indifferentengine/JankyTapeEcho/STL/Transport Mount.stl

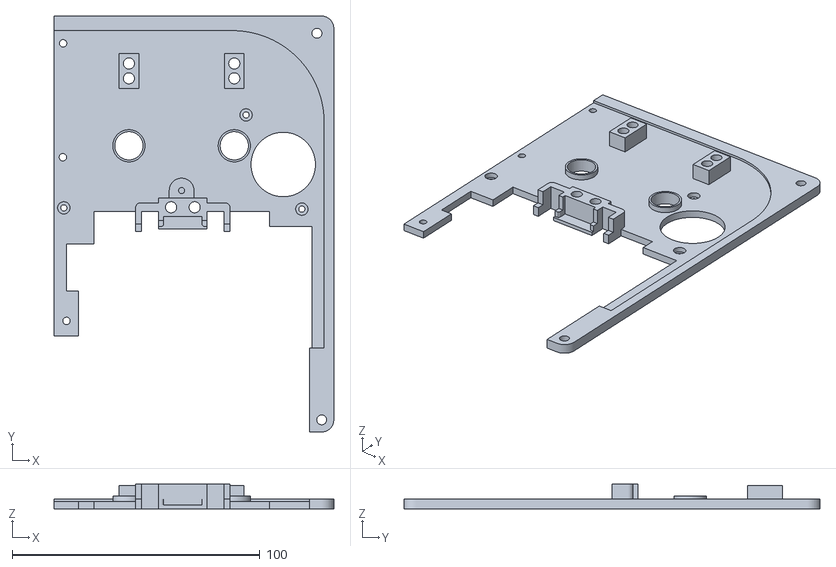
[picture p16: CAD file, 2023-03-04]
STL/Transport Mount.stl
112.8 x 167.8 x 10.0
